vineethjkatti-tech/iplanter/Assets/back_view.png

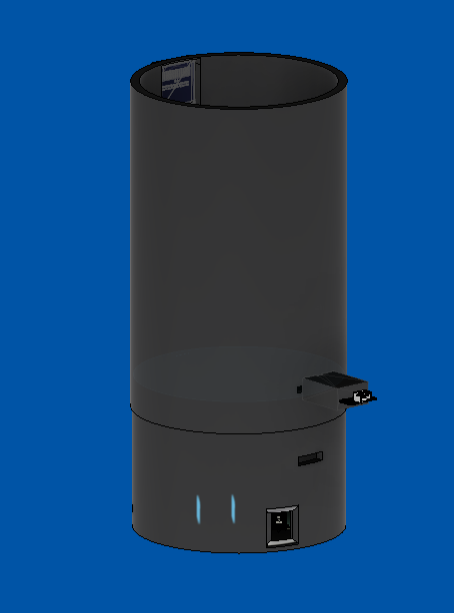
Assets/back_view.png
