vineethjkatti-tech/iplanter/Assets/bottom_view.png

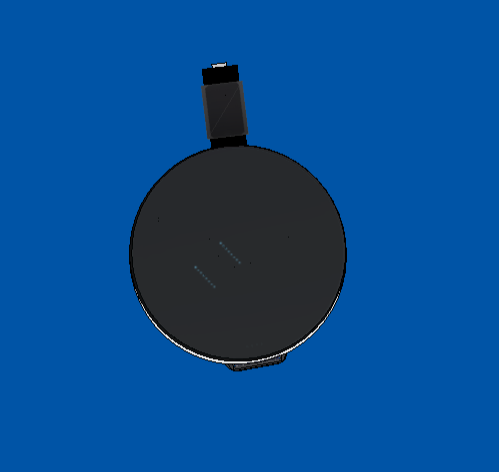
Assets/bottom_view.png
