vineethjkatti-tech/iplanter/Assets/front_view.png

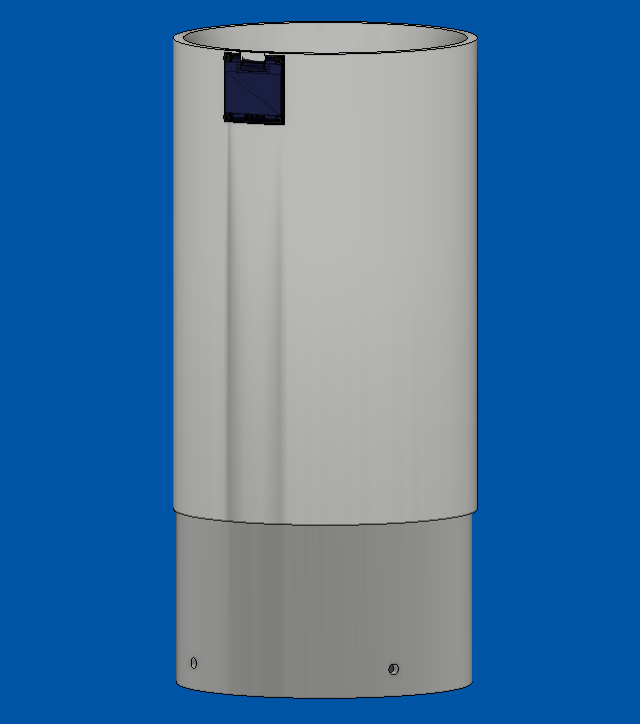
Assets/front_view.png
