vineethjkatti-tech/iplanter/Assets/hero_shot.png

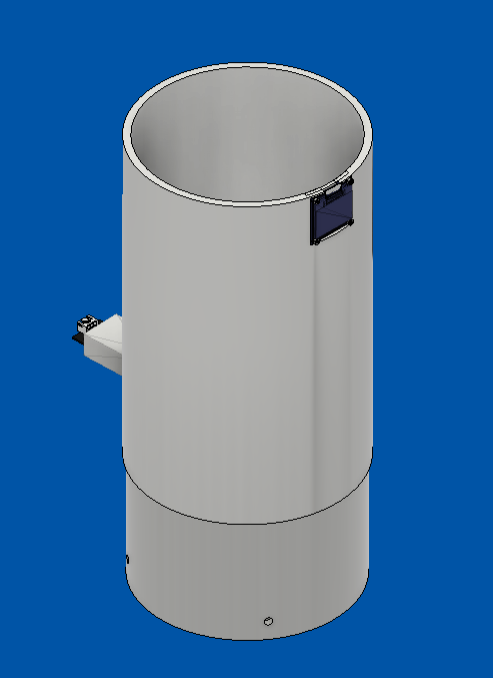
Assets/hero_shot.png
