vineethjkatti-tech/iplanter/Assets/pcb.png

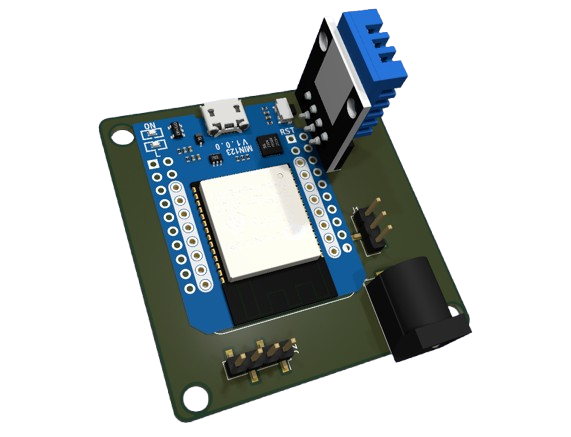
Assets/pcb.png
