vineethjkatti-tech/iplanter/Assets/pcb_bottom.png

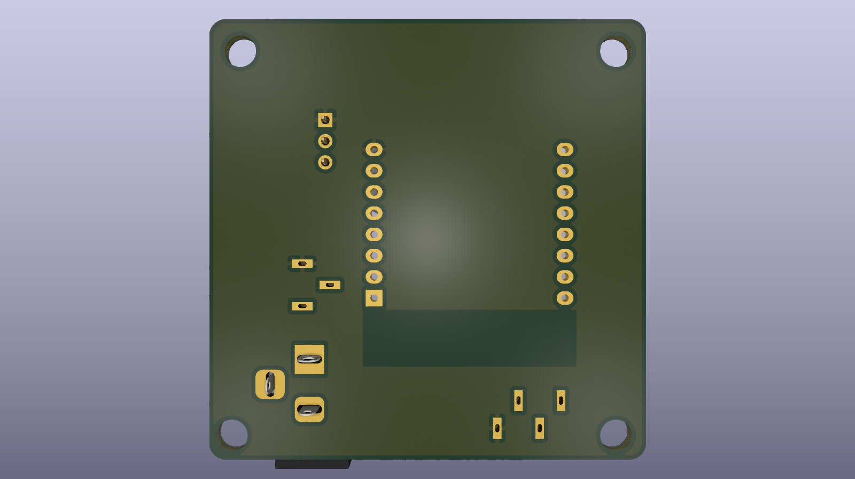
Assets/pcb_bottom.png
