vineethjkatti-tech/iplanter/Assets/pcb_schem.png

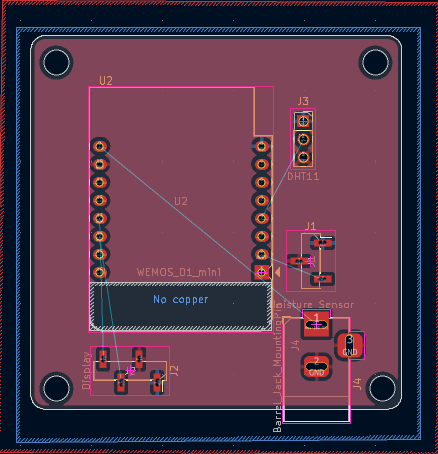
Assets/pcb_schem.png
