vineethjkatti-tech/iplanter/Assets/pcb_side.png

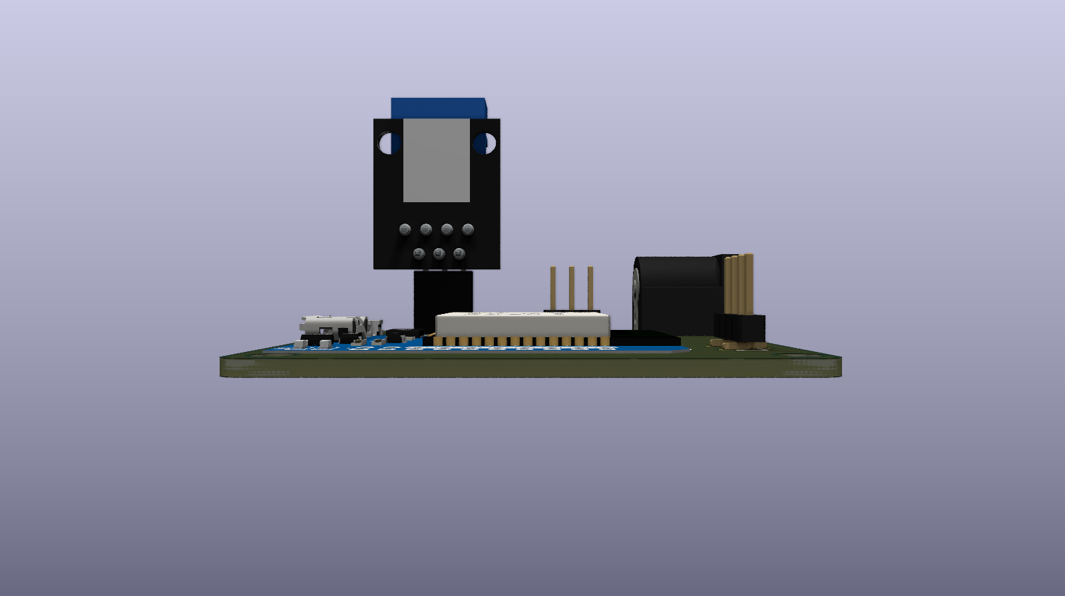
Assets/pcb_side.png
