vineethjkatti-tech/iplanter/Assets/pcb_top.png

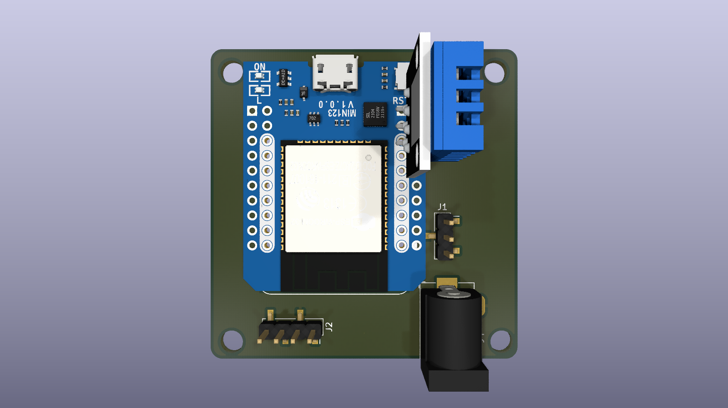
Assets/pcb_top.png
