vineethjkatti-tech/iplanter/Assets/top_view.png

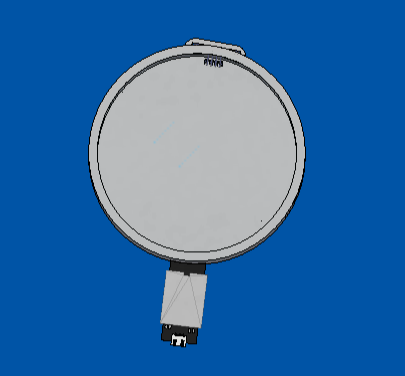
Assets/top_view.png
